fablabromagna-org/FLR-MKeyboards/khor_r12/3Dfiles/khor_case_it01/img2.jpg

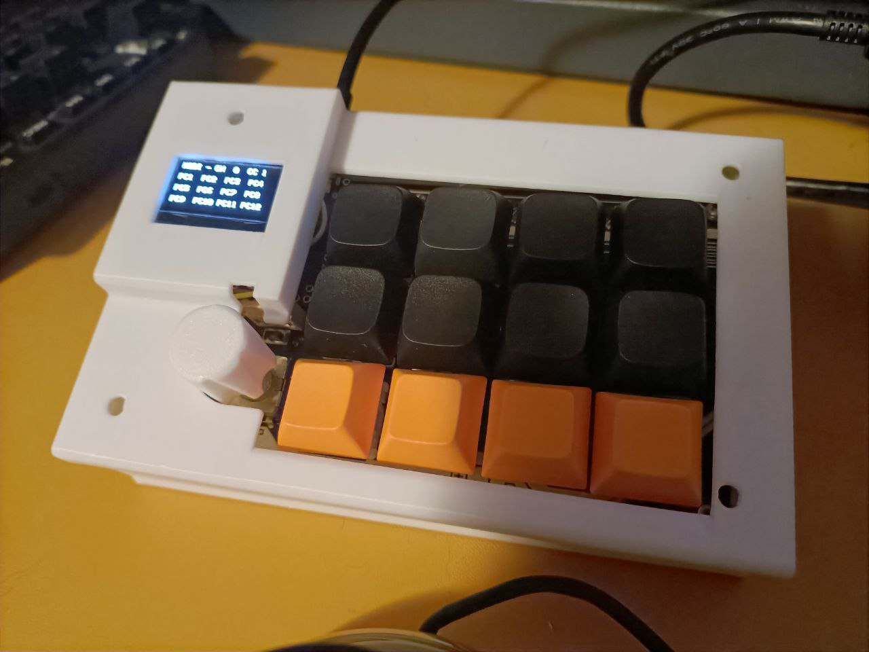
khor_r12/3Dfiles/khor_case_it01/img2.jpg
